dawsonjon/PicoRX/simulations/qsd_animation/fft_animation.gif

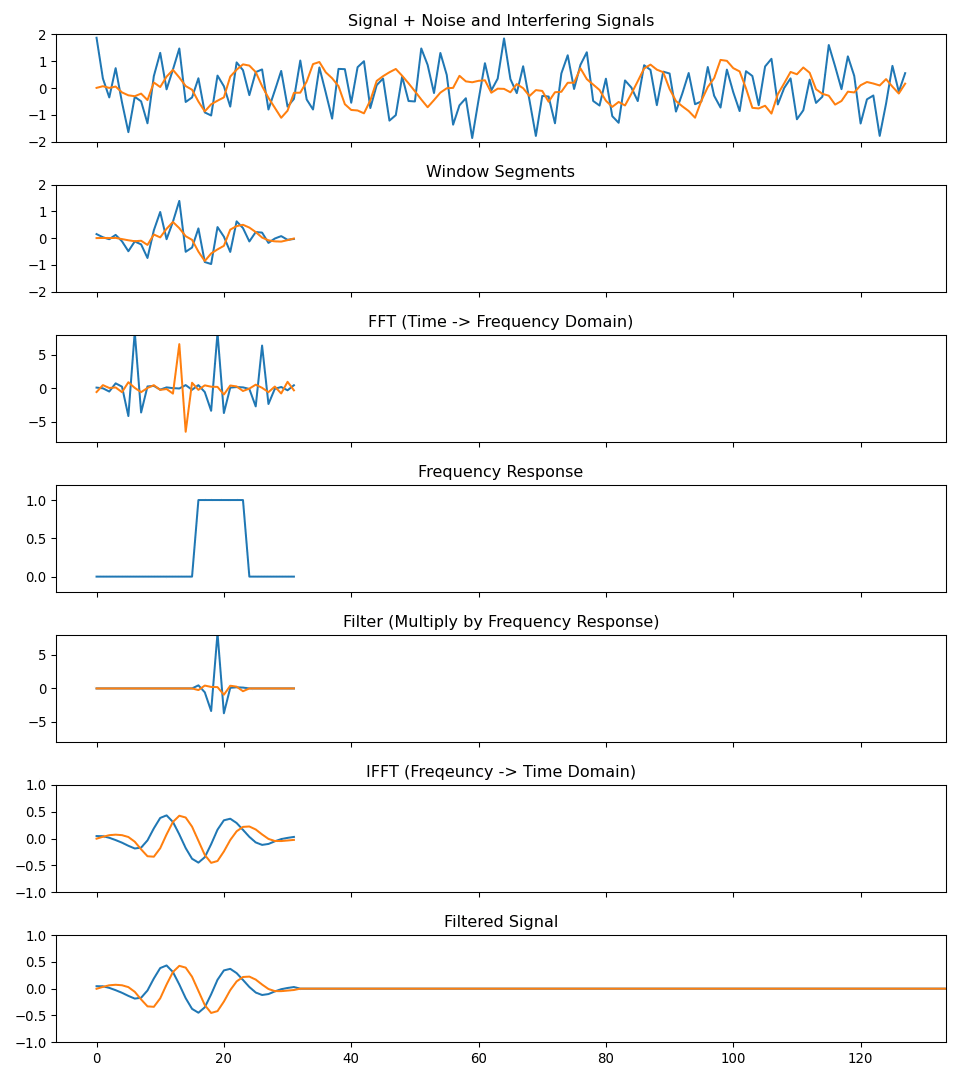
simulations/qsd_animation/fft_animation.gif
