dawsonjon/PicoRX/PCB/concept/concept.kicad_sch

## KiCad design PCB/concept/concept.kicad_sch (2026-02-28)

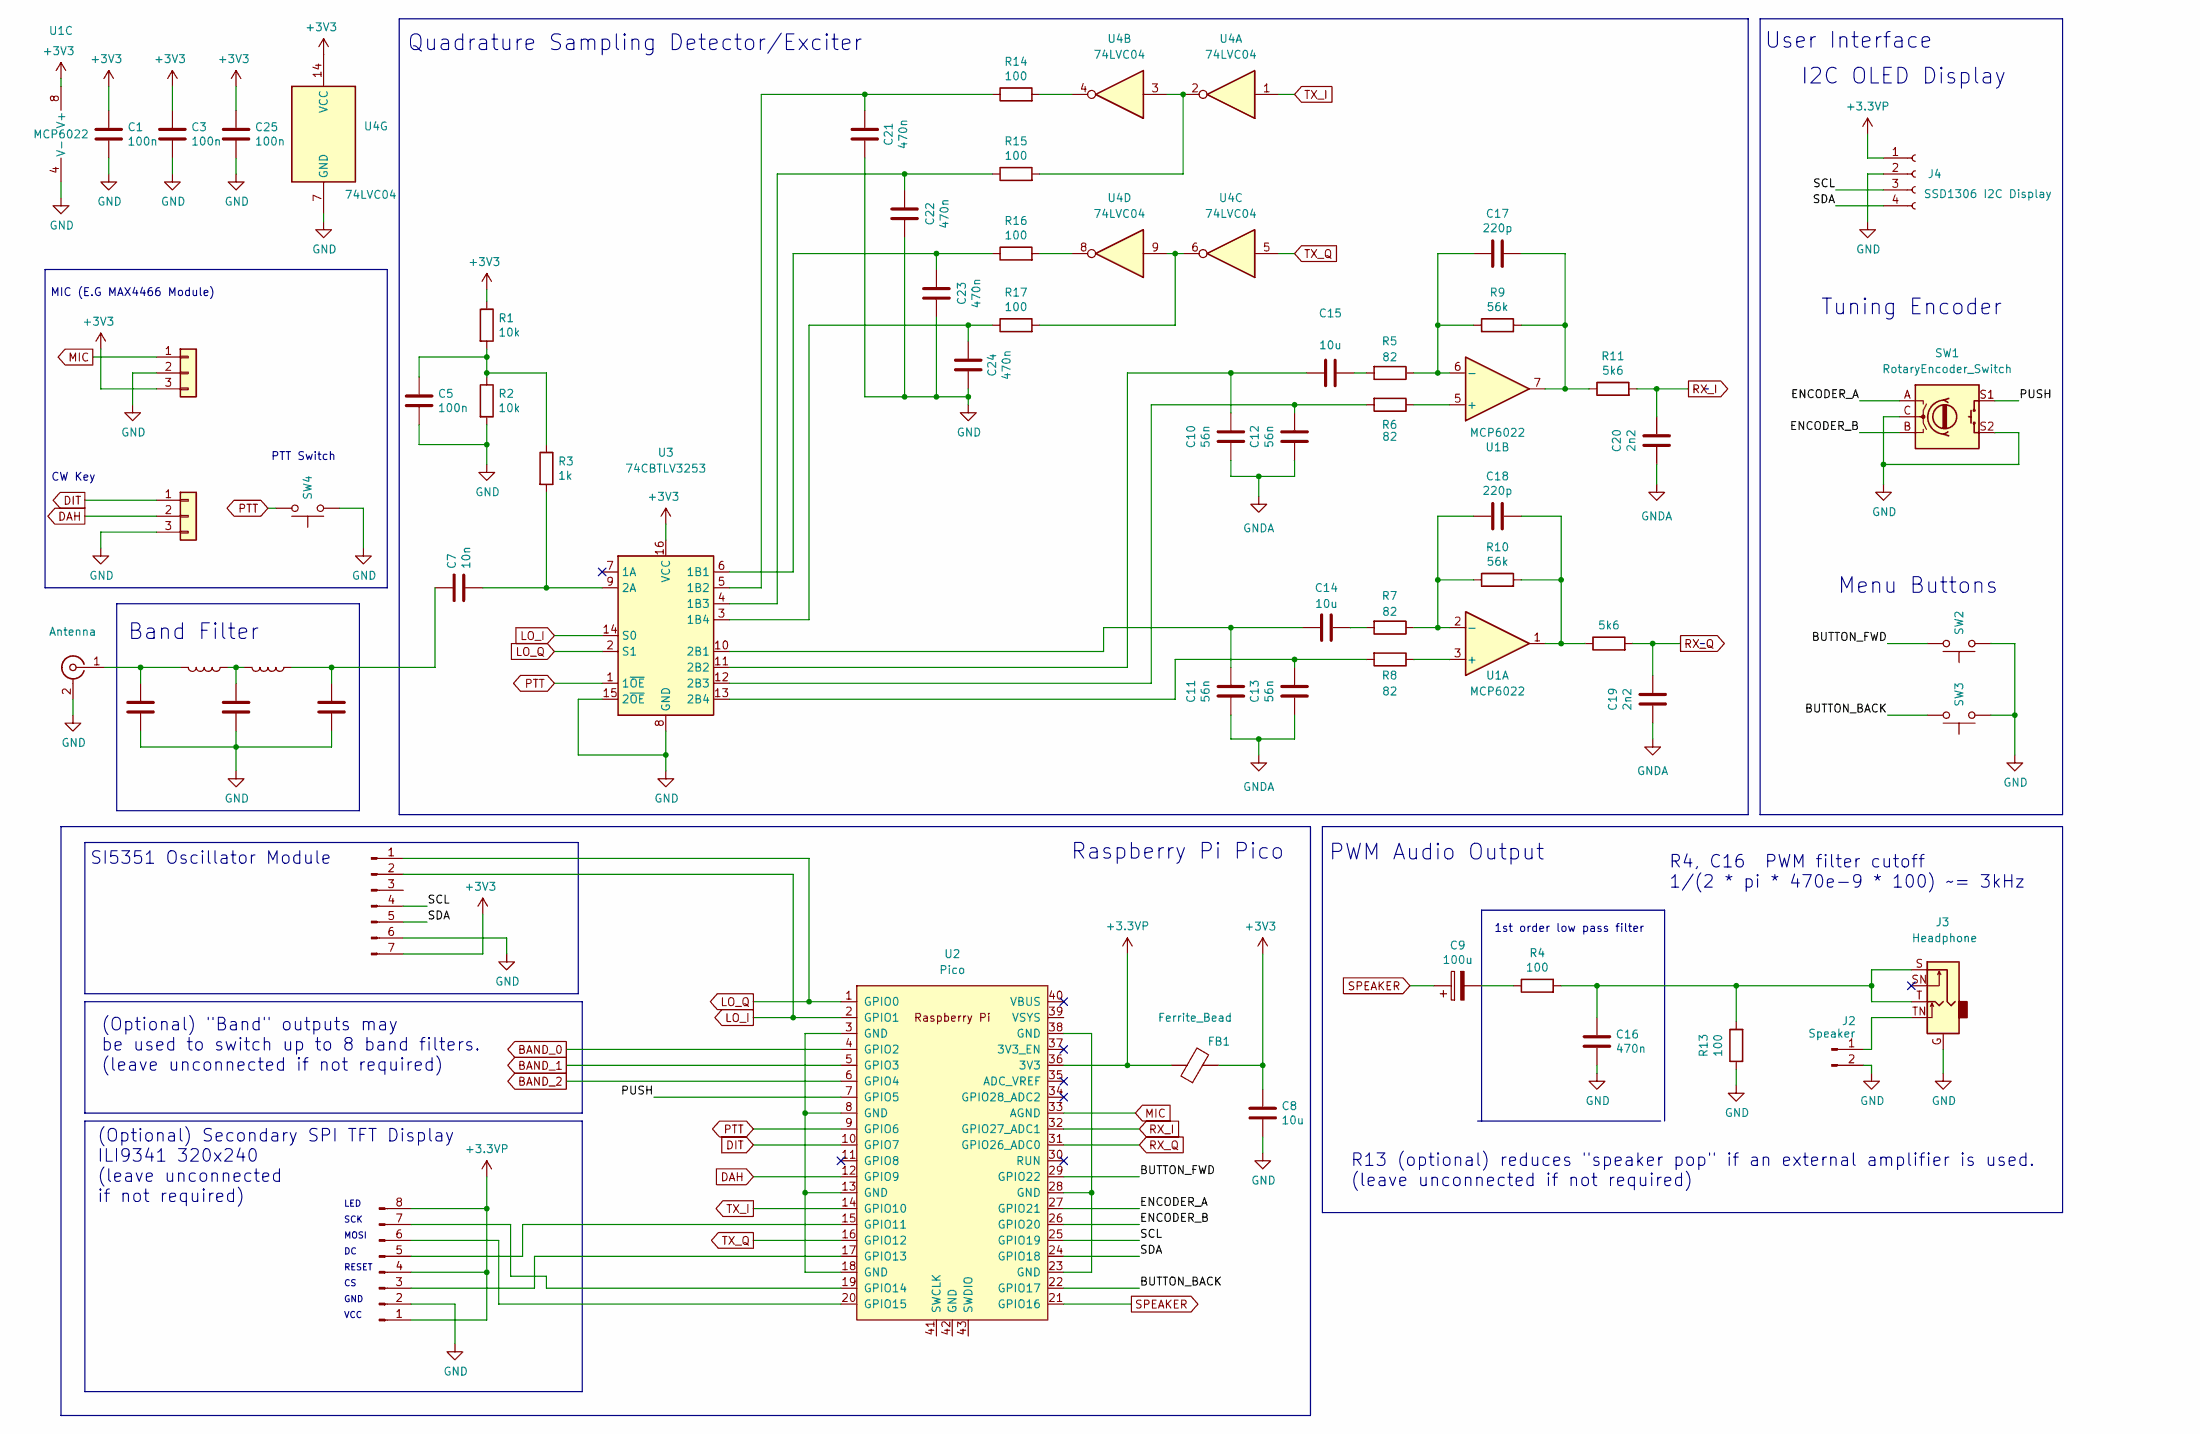
[picture p25: schematic concept.kicad_sch]

Parts:
C1, C3, C5, C25: 100n; C_0805_2012Metric
C2, C6: 680p; C_0805_2012Metric
C4: 1n; C_0805_2012Metric
C7: 10n; C_0805_2012Metric
C8, C14, C15: 10u; C_0805_2012Metric
C9: 100u; CP_EIA-3528-21_Kemet-B
C10, C11, C12, C13: 56n; C_0805_2012Metric
C16, C21, C22, C23, C24: 470n; C_0805_2012Metric
C17, C18: 220p; C_0805_2012Metric
C19, C20: 2n2; C_0805_2012Metric
FB1: Ferrite_Bead; L_0805_2012Metric
J1: Antenna; SMA_Samtec_SMA-J-P-X-ST-EM1_EdgeMount
J2: Speaker; PinHeader_1x02_P2.54mm_Vertical
J3: Headphone; jack3.5mm switched
J4: SSD1306 I2C Display; SDD1306
J5: Conn_01x08_Pin
J6: Conn_01x07_Pin
J7, J8: Conn_01x03
L1, L2: 330n; L_0805_2012Metric_Pad1.05x1.20mm_HandSolder
R1, R2: 10k; R_0805_2012Metric
R3: 1k; R_0805_2012Metric
R4, R13, R14, R15, R16, R17: 100; R_0805_2012Metric
R5, R6, R7, R8: 82; R_0805_2012Metric
R9, R10: 56k; R_0805_2012Metric
R11, R12: 5k6; R_0805_2012Metric
SW1: RotaryEncoder_Switch; RotaryEncoder_Alps_EC11E-Switch_Vertical_H20mm
SW2, SW3, SW4: SW_Push; SW_Tactile_SPST_Angled_PTS645Vx31-2LFS
U1: MCP6022; MSOP-8-1EP_3x3mm_P0.65mm_EP1.68x1.88mm
U2: Pico; RPi_Pico_SMD_TH
U3: 74CBTLV3253; SOIC-16_3.9x9.9mm_P1.27mm
U4: 74LVC04

Connections:
+3.3VP: FB1.1, J4.1, J5.1, J5.4, J5.8, U2.36 (3V3)
+3V3: C1.1, C3.1, C8.1, C25.1, FB1.2, J6.7, J7.3, R1.1, U1.8 (V+), U3.16 (VCC), U4.14 (VCC)
BAND_0: U2.4 (GPIO2)
BAND_1: U2.5 (GPIO3)
BAND_2: U2.6 (GPIO4)
BUTTON_BACK: SW3.2, U2.22 (GPIO17)
BUTTON_FWD: SW2.2, U2.29 (GPIO22)
DAH: J8.2, U2.12 (GPIO9)
DIT: J8.1, U2.10 (GPIO7)
ENCODER_A: SW1.A, U2.27 (GPIO21)
ENCODER_B: SW1.B, U2.26 (GPIO20)
GND: C1.2, C2.1, C3.2, C4.1, C5.2, C6.1, C8.2, C16.2, C21.1, C22.1, C23.1, C24.1, C25.2, J1.2 (Ext), J2.2, J3.G, J4.2, J5.2, J6.6, J7.2, J8.3, R2.2, R13.1, SW1.C, SW1.S2, SW2.1, SW3.1, SW4.1, U1.4 (V-), U3.8 (GND), U3.15 (2~OE), U4.7 (GND)
GNDA: C10.1, C11.1, C12.1, C13.1, C19.1, C20.1
LO_I: J6.2, U2.2 (GPIO1), U3.14 (S0)
LO_Q: J6.1, U2.1 (GPIO0), U3.2 (S1)
MIC: J7.1, U2.33 (AGND)
unnamed: C2.2, J1.1 (In), L1.2
unnamed: C4.2, L1.1, L2.2
unnamed: C5.1, R1.2, R2.1, R3.1
unnamed: C6.2, C7.1, L2.1
unnamed: C7.2, R3.2, U3.9 (2A)
unnamed: C9.2, R4.1
unnamed: C10.2, C15.2, U3.11 (2B2)
unnamed: C11.2, C14.2, U3.10 (2B1)
unnamed: C12.2, R6.2, U3.12 (2B3)
unnamed: C13.2, R8.2, U3.13 (2B4)
unnamed: C14.1, R7.2
unnamed: C15.1, R5.2
unnamed: C16.1, J3.S, J3.T, R4.2, R13.2
unnamed: C17.1, R5.1, R9.1, U1.6 (-)
unnamed: C17.2, R9.2, R11.1, U1.7
unnamed: C18.1, R7.1, R10.1, U1.2 (-)
unnamed: C18.2, R10.2, R12.1, U1.1
unnamed: C21.2, R14.1, U3.5 (1B2)
unnamed: C22.2, R15.1, U3.4 (1B3)
unnamed: C23.2, R16.1, U3.6 (1B1)
unnamed: C24.2, R17.1, U3.3 (1B4)
unnamed: J2.1, J3.TN
unnamed: J5.3, U2.17 (GPIO13)
unnamed: J5.5, U2.15 (GPIO11)
unnamed: J5.6, U2.20 (GPIO15)
unnamed: J5.7, U2.19 (GPIO14)
unnamed: R6.1, U1.5 (+)
unnamed: R8.1, U1.3 (+)
unnamed: R14.2, U4.4
unnamed: R15.2, U4.2, U4.3
unnamed: R16.2, U4.8
unnamed: R17.2, U4.6, U4.9
unnamed: U2.3 (GND), U2.8 (GND), U2.13 (GND), U2.18 (GND)
unnamed: U2.23 (GND), U2.28 (GND), U2.38 (GND)
PTT: SW4.2, U2.9 (GPIO6), U3.1 (1~OE)
PUSH: SW1.S1, U2.7 (GPIO5)
RX_I: C20.2, R11.2, U2.32 (GPIO27_ADC1)
RX_Q: C19.2, R12.2, U2.31 (GPIO26_ADC0)
SCL: J4.3, J6.4, U2.25 (GPIO19)
SDA: J4.4, J6.5, U2.24 (GPIO18)
SPEAKER: C9.1, U2.21 (GPIO16)
TX_I: U2.14 (GPIO10), U4.1
TX_Q: U2.16 (GPIO12), U4.5

Notes on the sheet:
Band Filter
LED
Raspberry Pi Pico
PWM Audio Output
CW Key
SI5351 Oscillator Module
Menu Buttons
I2C OLED Display
R13 (optional) reduces "speaker pop" if an external amplifier is used. (leave unconnected if not required)
PTT Switch
RESET
Quadrature Sampling Detector/Exciter
GND
MIC (E.G MAX4466 Module)
(Optional) "Band" outputs may be used to switch up to 8 band filters. (leave unconnected if not required)
R4, C16 PWM filter cutoff 1/(2 * pi * 470e-9 * 100) ~= 3kHz
1st order low pass filter
Tuning Encoder
VCC
MOSI
SCK
(Optional) Secondary SPI TFT Display ILI9341 320x240 (leave unconnected if not required)
User Interface
