dawsonjon/PicoRX/PCB/pico_rx/Bandpass.kicad_sch

## KiCad design PCB/pico_rx/Bandpass.kicad_sch (2023-07-05)

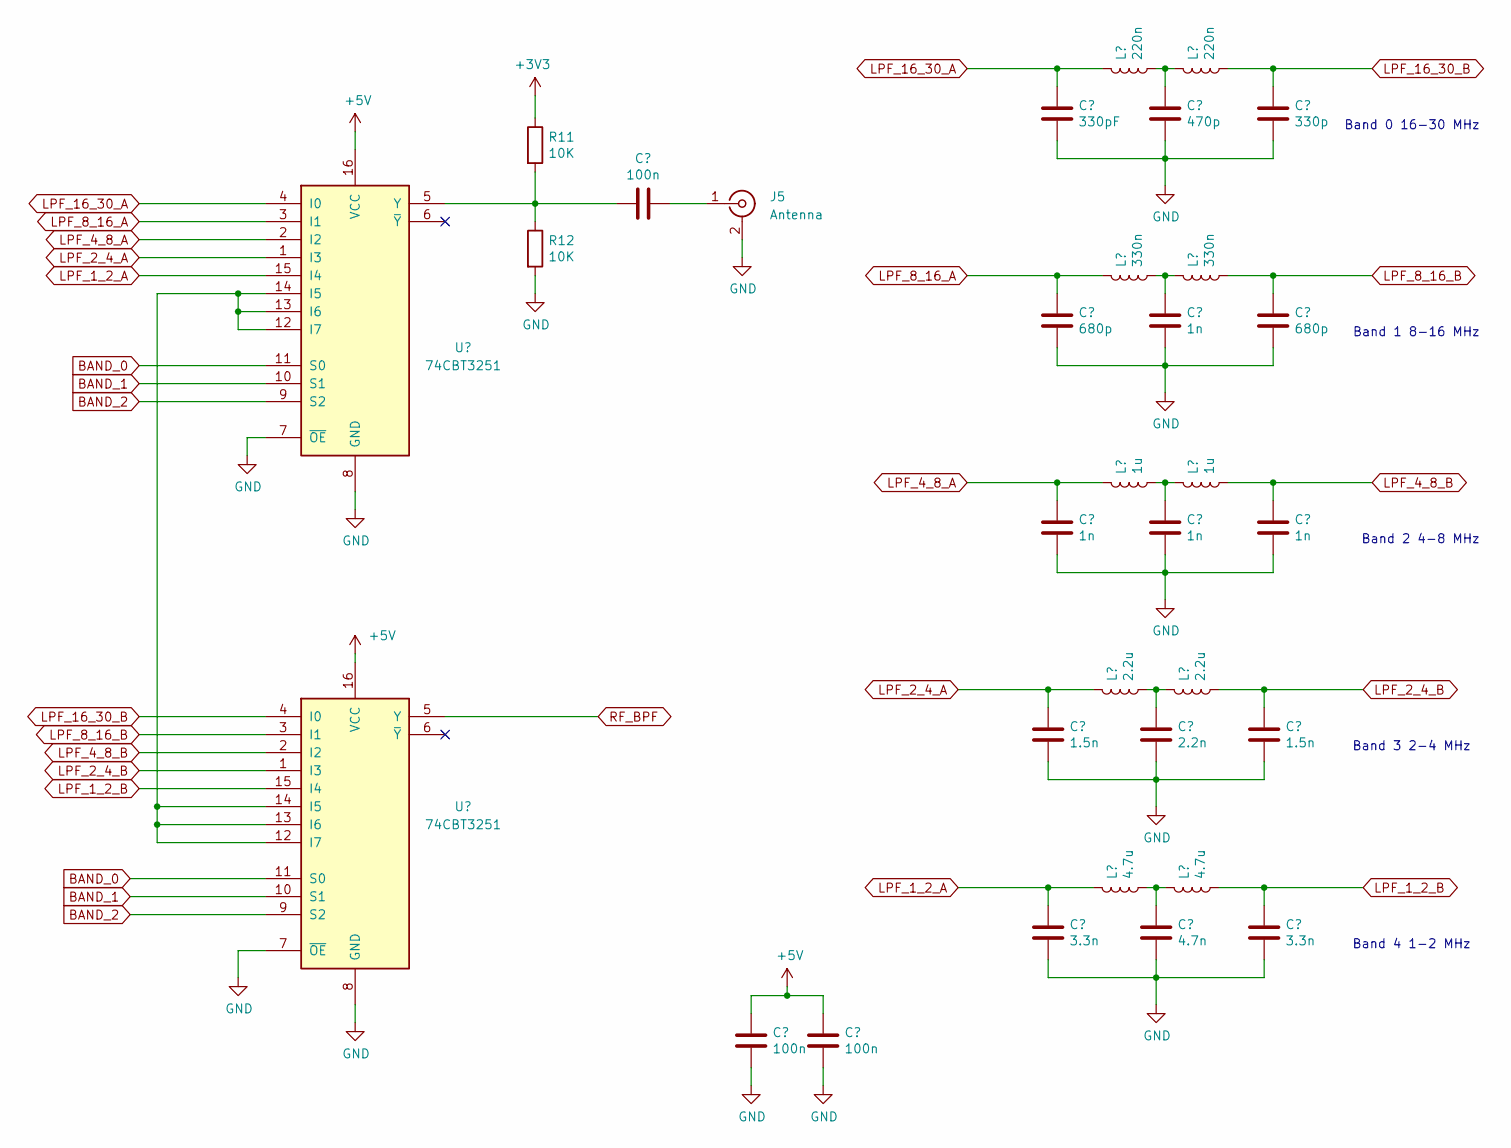
[picture p26: schematic Bandpass.kicad_sch]

Parts:
C1, C2, C3: 100n; C_0805_2012Metric
C6, C9: 680p; C_0805_2012Metric
C7, C13, C14, C15: 1n; C_0805_2012Metric
C8: 330pF; C_0805_2012Metric
C12: 470p; C_0805_2012Metric
C16: 330p; C_0805_2012Metric
C19, C22: 1.5n; C_0805_2012Metric
C21: 2.2n; C_0805_2012Metric
C36, C38: 3.3n; C_0805_2012Metric
C37: 4.7n; C_0805_2012Metric
J5: Antenna; SMA_Amphenol_132289_EdgeMount
L1, L2: 330n; L_0805_2012Metric_Pad1.05x1.20mm_HandSolder
L3, L4: 1u; L_0805_2012Metric_Pad1.05x1.20mm_HandSolder
L5, L13: 220n; L_0805_2012Metric_Pad1.05x1.20mm_HandSolder
L6, L7: 2.2u; L_0805_2012Metric_Pad1.05x1.20mm_HandSolder
L8, L9: 4.7u; L_0805_2012Metric_Pad1.05x1.20mm_HandSolder
R11, R12: 10K; R_0805_2012Metric
U1, U2: 74CBT3251; SOIC-16_3.9x9.9mm_P1.27mm

Connections:
+3V3: R11.1
+5V: C2.1, C3.1, U1.16 (VCC), U2.16 (VCC)
BAND_0: U1.11 (S0), U2.11 (S0)
BAND_1: U1.10 (S1), U2.10 (S1)
BAND_2: U1.9 (S2), U2.9 (S2)
GND: C2.2, C3.2, C6.1, C7.1, C8.1, C9.1, C12.1, C13.1, C14.1, C15.1, C16.1, C19.1, C21.1, C22.1, C36.1, C37.1, C38.1, J5.2 (Ext), R12.2, U1.7 (~OE), U1.8 (GND), U2.7 (~OE), U2.8 (GND)
LPF_1_2_A: C36.2, L8.2, U1.15 (I4)
LPF_1_2_B: C38.2, L9.1, U2.15 (I4)
LPF_2_4_A: C19.2, L6.2, U1.1 (I3)
LPF_2_4_B: C22.2, L7.1, U2.1 (I3)
LPF_4_8_A: C13.2, L3.2, U1.2 (I2)
LPF_4_8_B: C15.2, L4.1, U2.2 (I2)
LPF_8_16_A: C6.2, L1.2, U1.3 (I1)
LPF_8_16_B: C9.2, L2.1, U2.3 (I1)
LPF_16_30_A: C8.2, L13.2, U1.4 (I0)
LPF_16_30_B: C16.2, L5.1, U2.4 (I0)
unnamed: C1.1, J5.1 (In)
unnamed: C1.2, R11.2, R12.1, U1.5 (Y)
unnamed: C7.2, L1.1, L2.2
unnamed: C12.2, L5.2, L13.1
unnamed: C14.2, L3.1, L4.2
unnamed: C21.2, L6.1, L7.2
unnamed: C37.2, L8.1, L9.2
unnamed: U1.12 (I7), U1.13 (I6), U1.14 (I5), U2.12 (I7), U2.13 (I6), U2.14 (I5)
RF_BPF: U2.5 (Y)

Notes on the sheet:
Band 2 4-8 MHz
Band 4 1-2 MHz
Band 1 8-16 MHz
Band 3 2-4 MHz
Band 0 16-30 MHz
