dawsonjon/PicoRX/tusb_config.h

/*
 * The MIT License (MIT)
 *
 * Copyright (c) 2019 Ha Thach (tinyusb.org)
 *
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
 */

#ifndef _TUSB_CONFIG_H_
#define _TUSB_CONFIG_H_

#include "usb_descriptors.h"

#ifdef __cplusplus
extern "C" {
#endif

//--------------------------------------------------------------------
// COMMON CONFIGURATION
//--------------------------------------------------------------------

// defined by compiler flags for flexibility
#ifndef CFG_TUSB_MCU
#error CFG_TUSB_MCU must be defined
#endif

#if CFG_TUSB_MCU == OPT_MCU_LPC43XX || CFG_TUSB_MCU == OPT_MCU_LPC18XX || CFG_TUSB_MCU == OPT_MCU_MIMXRT10XX
#define CFG_TUSB_RHPORT0_MODE       (OPT_MODE_DEVICE | OPT_MODE_HIGH_SPEED)
#else
#define CFG_TUSB_RHPORT0_MODE       OPT_MODE_DEVICE
#endif

#ifndef CFG_TUSB_OS
#define CFG_TUSB_OS                 OPT_OS_NONE
#endif

#ifndef CFG_TUSB_DEBUG
#define CFG_TUSB_DEBUG              0
#endif

// CFG_TUSB_DEBUG is defined by compiler in DEBUG build
// #define CFG_TUSB_DEBUG           0

/* USB DMA on some MCUs can only access a specific SRAM region with restriction on alignment.
 * Tinyusb use follows macros to declare transferring memory so that they can be put
 * into those specific section.
 * e.g
 * - CFG_TUSB_MEM SECTION : __attribute__ (( section(".usb_ram") ))
 * - CFG_TUSB_MEM_ALIGN   : __attribute__ ((aligned(4)))
 */
#ifndef CFG_TUSB_MEM_SECTION
#define CFG_TUSB_MEM_SECTION
#endif

#ifndef CFG_TUSB_MEM_ALIGN
#define CFG_TUSB_MEM_ALIGN          __attribute__ ((aligned(4)))
#endif

//--------------------------------------------------------------------
// DEVICE CONFIGURATION
//--------------------------------------------------------------------

#ifndef CFG_TUD_ENDPOINT0_SIZE
#define CFG_TUD_ENDPOINT0_SIZE    (64)
#endif

//------------- CLASS -------------//
#define CFG_TUD_CDC               1
#define CFG_TUD_MSC               0
#define CFG_TUD_HID               0
#define CFG_TUD_MIDI              0
#define CFG_TUD_AUDIO             1
#define CFG_TUD_VENDOR            0

//--------------------------------------------------------------------
// AUDIO CLASS DRIVER CONFIGURATION
//--------------------------------------------------------------------

// Have a look into audio_device.h for all configurations

#define CFG_TUD_AUDIO_FUNC_1_SAMPLE_RATE                              (15000) // make sure this matches rx_definitions.h:audio_sample_rate
#define CFG_TUD_AUDIO_FUNC_1_DESC_LEN                                 TUD_AUDIO_PICORX_DESC_LEN
#define CFG_TUD_AUDIO_FUNC_1_N_AS_INT                                 1                                       // Number of Standard AS Interface Descriptors (4.9.1) defined per audio function - this is required to be able to remember the current alternate settings of these interfaces - We restrict us here to have a constant number for all audio functions (which means this has to be the maximum number of AS interfaces an audio function has and a second audio function with less AS interfaces just wastes a few bytes)
#define CFG_TUD_AUDIO_FUNC_1_CTRL_BUF_SZ                              64                                      // Size of control request buffer

#define CFG_TUD_AUDIO_ENABLE_EP_IN                                    1
#define CFG_TUD_AUDIO_FUNC_1_N_BYTES_PER_SAMPLE_TX                    2                                       // Driver gets this info from the descriptors - we define it here to use it to setup the descriptors and to do calculations with it below
#define CFG_TUD_AUDIO_FUNC_1_N_CHANNELS_TX                            2                                       // Driver gets this info from the descriptors - we define it here to use it to setup the descriptors and to do calculations with it below - be aware: for different number of channels you need another descriptor!
#define CFG_TUD_AUDIO_EP_SZ_IN                                        TUD_AUDIO_EP_SIZE(CFG_TUD_AUDIO_FUNC_1_SAMPLE_RATE, CFG_TUD_AUDIO_FUNC_1_N_BYTES_PER_SAMPLE_TX, CFG_TUD_AUDIO_FUNC_1_N_CHANNELS_TX)
#define CFG_TUD_AUDIO_FUNC_1_EP_IN_SZ_MAX                             CFG_TUD_AUDIO_EP_SZ_IN                  // Maximum EP IN size for all AS alternate settings used
#define CFG_TUD_AUDIO_FUNC_1_EP_IN_SW_BUF_SZ                          (TUD_OPT_HIGH_SPEED ? 16 : 2) * CFG_TUD_AUDIO_EP_SZ_IN

// CDC FIFO size of TX and RX
#define CFG_TUD_CDC_RX_BUFSIZE                    64
#define CFG_TUD_CDC_TX_BUFSIZE                    64

#ifdef __cplusplus
}
#endif

#endif /* _TUSB_CONFIG_H_ */
