dawsonjon/PicoRX/src/rx_dsp.cpp

#include "rx_dsp.h"
#include "rx_definitions.h"
#include "fft_filter.h"
#include "utils.h"
#include "pico/stdlib.h"
#include "cic_corrections.h"

#include <math.h>
#include <cstdio>
#include <algorithm>

static const int16_t deemph_taps[2][3] = {{14430, 14430, -3909}, {10571, 10571, -11626}};
int16_t __not_in_flash_func(rx_dsp :: apply_deemphasis)(int16_t x)
{
if (deemphasis == 0) return x;

  static int16_t x1 = 0;
  static int16_t y1 = 0;
  static int16_t err = 0;

  const size_t i = deemphasis - 1;

  int32_t y = ((int32_t)x * deemph_taps[i][0]) +
              ((int32_t)x1 * deemph_taps[i][1]) -
              ((int32_t)y1 * deemph_taps[0][2]) + err;

  if (y > 0x1FFFFFFFL) {
    y = 0x1FFFFFFFL;
  }
  if (y < -0x20000000L) {
    y = -0x20000000L;
  }

  err = y & ((1 << 15) - 1);
  y >>= 15;
  x1 = x;
  y1 = y;
  return y;
}

int16_t __not_in_flash_func(rx_dsp ::apply_treble)(int16_t x) {
  static const int32_t treble_taps[4][2][3] = {
      {{26363, -36747, 14207}, {16383, -19828, 7267}},
      {{42359, -62303, 24741}, {16383, -18062, 6476}},
      {{67860, -104422, 42534}, {16383, -16114, 5703}},
      {{108241, -173031, 72157}, {16383, -13987, 4972}}};

  static int16_t x1 = 0;
  static int16_t y1 = 0;
  static int16_t x2 = 0;
  static int16_t y2 = 0;
  static int16_t err = 0;

  if (treble == 0) return x;

  const uint8_t i = treble - 1;

  x >>= 1;
  int32_t y = ((int32_t)x * treble_taps[i][0][0]) +
              ((int32_t)x1 * treble_taps[i][0][1]) +
              ((int32_t)x2 * treble_taps[i][0][2]) + err;
  y -= ((int32_t)y1 * treble_taps[i][1][1]) +
       ((int32_t)y2 * treble_taps[i][1][2]);

  if (y > 0xFFFFFFFL) {
    y = 0xFFFFFFFL;
  }
  if (y < -0x10000000L) {
    y = -0x10000000L;
  }

  err = y & ((1 << 14) - 1);
  y >>= 14;

  x2 = x1;
  x1 = x;
  y2 = y1;
  y1 = y;
  return y << 1;
}

int16_t __not_in_flash_func(rx_dsp ::apply_bass)(int16_t x) {
  static const int32_t bass_taps[4][2][3] = {
      {{16808, -30178, 13691}, {16383, -30248, 14045}},
      {{17253, -30437, 13616}, {16383, -30584, 14338}},
      {{17728, -30637, 13490}, {16383, -30876, 14596}},
      {{18245, -30777, 13313}, {16383, -31129, 14824}}};

  static int16_t x1 = 0;
  static int16_t y1 = 0;
  static int16_t x2 = 0;
  static int16_t y2 = 0;
  static int16_t err = 0;

  if (bass == 0) return x;

  const uint8_t i = bass - 1;

  x >>= 1;
  int32_t y = ((int32_t)x * bass_taps[i][0][0]) +
              ((int32_t)x1 * bass_taps[i][0][1]) +
              ((int32_t)x2 * bass_taps[i][0][2]) + err;
  y -= ((int32_t)y1 * bass_taps[i][1][1]) + ((int32_t)y2 * bass_taps[i][1][2]);

  if (y > 0xFFFFFFFL) {
    y = 0xFFFFFFFL;
  }
  if (y < -0x10000000L) {
    y = -0x10000000L;
  }

  err = y & ((1 << 14) - 1);
  y >>= 14;

  x2 = x1;
  x1 = x;
  y2 = y1;
  y1 = y;
  return y << 1;
}

void __not_in_flash_func(rx_dsp ::apply_impulse_blanker)(int16_t &i, int16_t &q,
                                                         uint16_t mag) {
  static uint32_t avg_g = 32767;
  static uint32_t avg_mag;
  const uint32_t thres_lut[6] = {98301, 91748, 85194, 78641,
                                 72087, 65534};  // 3.0 to 2.0 in 0.2 steps

  if(impulse_threshold == 0)
  {
    return;
  }

  avg_mag += mag - (avg_mag / 4096);
  const uint32_t a_mag = avg_mag / 4096;

  const uint32_t thr = thres_lut[impulse_threshold - 1];

  uint32_t g = 32767;
  if (mag > ((a_mag * thr) >> 15)) {
    g = (a_mag << 15) / mag;
  }
  avg_g += g - avg_g / 8;
  g = avg_g / 8;

  if (g < 32767) {
    i = (g * i) >> 15;
    q = (g * q) >> 15;
  }
}

static uint32_t __not_in_flash_func(intsqrt)(const uint32_t n) {
    uint8_t shift = 32u;
    shift += shift & 1; // round up to next multiple of 2

    uint32_t result = 0;

    do {
        shift -= 2;
        result <<= 1; // leftshift the result to make the next guess
        result |= 1;  // guess that the next bit is 1
        result ^= result * result > (n >> shift); // revert if guess too high
    } while (shift != 0);

    return result;
}

void inline rx_dsp :: iq_imbalance_correction(int16_t &i, int16_t &q)
{
    if (iq_correction)
    {
      static uint16_t index = 0;
      static int32_t theta1 = 0;
      static int32_t theta2 = 0;
      static int32_t theta3 = 0;

      theta1 += ((i < 0) ? -q : q);
      theta2 += ((i < 0) ? -i : i);
      theta3 += ((q < 0) ? -q : q);

      static int32_t c1 = 0;
      static int32_t c2 = 0;
      if (++index == 512)
      {
        static int64_t theta1_filtered = 0;
        static int64_t theta2_filtered = 0;
        static int64_t theta3_filtered = 0;
        theta1_filtered = theta1_filtered - (theta1_filtered >> 5) + (-theta1 >> 5);
        theta2_filtered = theta2_filtered - (theta2_filtered >> 5) + (theta2 >> 5);
        theta3_filtered = theta3_filtered - (theta3_filtered >> 5) + (theta3 >> 5);

        //try to constrain square to less than 32 bits.
        //Assue that i/q used full int16_t range.
        //Accumulating 512 samples adds 9 bits of growth, so remove 18 after square.
        const int64_t theta1_squared = (theta1_filtered * theta1_filtered) >> 18;
        const int64_t theta2_squared = (theta2_filtered * theta2_filtered) >> 18;
        const int64_t theta3_squared = (theta3_filtered * theta3_filtered) >> 18;

        c1 = (theta1_filtered << 15)/theta2_filtered;
        c2 = intsqrt(((theta3_squared - theta1_squared) << 30)/theta2_squared);

        theta1 = 0;
        theta2 = 0;
        theta3 = 0;
        index = 0;
      }

      q += ((int32_t)i * c1) >> 15;
      i = ((int32_t)i * c2) >> 15;
    }
}

uint16_t __not_in_flash_func(rx_dsp :: process_block)(uint16_t samples[], int16_t audio_samples[], ring_buffer_t *iq_samples)
{

  uint16_t decimated_index = 0;
  int16_t iq[2 * adc_block_size / cic_decimation_rate];

  for(uint16_t idx=0; idx<adc_block_size; idx++)
  {
      //convert to signed representation
      const int16_t raw_sample = samples[idx];

      //work out which samples are i and q
      int16_t i = ((idx&1)^1^swap_iq)*raw_sample;//even samples contain i data
      int16_t q = ((idx&1)^swap_iq)*raw_sample;//odd samples contain q data

      //reduce sample rate by a factor of 16
      if(decimate(i, q))
      {

        static uint32_t iq_count = 0;
        static int32_t i_accumulator = 0;
        static int32_t q_accumulator = 0;
        static int16_t i_avg = 0;
        static int16_t q_avg = 0;
        i_accumulator += i;
        q_accumulator += q;
        if (++iq_count == 2048) //power of 2 avoids division
        {
          i_avg = i_accumulator / 2048;
          q_avg = q_accumulator / 2048;
          i_accumulator = 0;
          q_accumulator = 0;
          iq_count = 0;
        }
        i -= i_avg;
        q -= q_avg;

        iq_imbalance_correction(i, q);

        //Apply frequency shift (move tuned frequency to DC)
        frequency_shift(i, q);

        #ifdef MEASURE_DC_BIAS
        static int64_t bias_measurement = 0;
        static int32_t num_bias_measurements = 0;
        if(num_bias_measurements == 100000) {
          printf("DC BIAS x 100 %lli\n", bias_measurement/1000);
          num_bias_measurements = 0;
          bias_measurement = 0;
        }
        else {
          num_bias_measurements++;
          bias_measurement += i;
        }
        #endif

        iq[decimated_index] = i;
        iq[decimated_index + 1] = q;
        decimated_index+=2;
      }
  }

  //fft filter decimates a further 2x
  //if the capture buffer isn't in use, fill it
  filter_control.capture = sem_try_acquire(&spectrum_semaphore);
  capture_filter_control = filter_control;
  fft_filter_inst.process_sample(iq, filter_control, capture);
  if(filter_control.capture) sem_release(&spectrum_semaphore);

  for(uint16_t idx=0; idx<adc_block_size/decimation_rate; idx++)
  {
    int16_t i = iq[2 * idx];
    int16_t q = iq[2 * idx + 1];

    uint32_t complex_sample = (uint32_t)i << 16 | ((uint32_t)q & 0xffff);
    queue_try_add(&data_queue, (void*)&complex_sample);

    //Measure amplitude (for signal strength indicator)
    uint16_t magnitude;
    int16_t _phase;
    rectangular_2_polar(i, q, &magnitude, &_phase);

    // Impulse noise blanker
    apply_impulse_blanker(i, q, magnitude);

    //Demodulate to give audio sample
    int32_t audio = demodulate(i, q, magnitude, _phase);

    //De-emphasis
    audio = apply_deemphasis(audio);

    // Bass
    audio = apply_bass(audio);

    // Treble
    audio = apply_treble(audio);

    //Automatic gain control scales signal to use full 16 bit range
    //e.g. -32767 to 32767
    audio = automatic_gain_control(audio);

    //squelch
    audio = squelch(audio);

    //output raw audio
    audio_samples[idx] = audio;
  }

  if (sem_try_acquire(&audio_semaphore)) {
    for (uint16_t idx = 0; idx < adc_block_size / decimation_rate; idx+=4) {
      audio_capture[audio_capture_idx * 16 + (idx / 4)] = audio_samples[idx];
    }
    audio_capture_idx++;
    if (audio_capture_idx == 8) {
      audio_capture_idx = 0;
    }
    sem_release(&audio_semaphore);
  }

  if (iq_samples) {
    ring_buffer_push_ovr(
        iq_samples, (uint8_t *)iq,
        2 * sizeof(int16_t) * adc_block_size / decimation_rate);
  }

  //average over the number of samples
  signal_amplitude = (filter_control.magnitude_sum * decimation_rate)/adc_block_size;

  return adc_block_size/decimation_rate;
}

void __not_in_flash_func(rx_dsp :: frequency_shift)(int16_t &i, int16_t &q)
{
    //Apply frequency shift (move tuned frequency to DC)
    const uint16_t scaled_phase = (phase >> 21);
    const int16_t rotation_i =  sin_table[(scaled_phase+512u) & 0x7ff]; //32 - 21 = 11MSBs
    const int16_t rotation_q = -sin_table[scaled_phase];

    phase += frequency;
    //truncating fractional bits introduces bias, but it is more efficient to remove it after decimation
    int32_t bias = (1<<14);
    const int16_t i_shifted = (((int32_t)i * rotation_i) - ((int32_t)q * rotation_q) + bias) >> 15;
    const int16_t q_shifted = (((int32_t)q * rotation_i) + ((int32_t)i * rotation_q) + bias) >> 15;

    i = i_shifted;
    q = q_shifted;
}

bool __not_in_flash_func(rx_dsp :: decimate)(int16_t &i, int16_t &q)
{
      static int32_t integratori4d5 = 0;
      static int32_t integratorq4d5 = 0;

      //CIC decimation filter
      //implement integrator stages
      integratori1 += i;
      integratorq1 += q;
      integratori2 += integratori1;
      integratorq2 += integratorq1;
      integratori3 += integratori2;
      integratorq3 += integratorq2;
      integratori4 += integratori3;
      integratorq4 += integratorq3;

      decimate_count++;
      if(decimate_count == (cic_decimation_rate-5))
      {
        integratori4d5 = integratori4;
        integratorq4d5 = integratorq4;
      }
      else if(decimate_count >= cic_decimation_rate)
      {
        decimate_count = 0;

        //implement comb stages
        const int32_t combi1 = integratori4-delayi0;
        const int32_t combq1 = integratorq4-delayq0;
        const int32_t combi2 = combi1-delayi1;
        const int32_t combq2 = combq1-delayq1;
        const int32_t combi3 = combi2-delayi2;
        const int32_t combq3 = combq2-delayq2;
        const int32_t combi4 = combi3-delayi3;
        const int32_t combq4 = combq3-delayq3;
        delayi0 = integratori4d5;
        delayq0 = integratorq4d5;
        delayi1 = combi1;
        delayq1 = combq1;
        delayi2 = combi2;
        delayq2 = combq2;
        delayi3 = combi3;
        delayq3 = combq3;

        //remove bit growth, but keep some extra bits since noise floor is now lower
        i = combi4>>(cic_bit_growth-extra_bits);
        q = combq4>>(cic_bit_growth-extra_bits);

        return true;
      }

      return false;
}

// For the formulas see 'PicoRX/simulations/am_sync_des.py:pll_3rd_order_des'
// PLL loop bandwidth: 30Hz
#define AMSYNC_NUM_TAPS (3)
#define AMSYNC_B0 (1160)
#define AMSYNC_B1 (-2306)
#define AMSYNC_B2 (1146)
#define AMSYNC_A0 (32767)
#define AMSYNC_A1 (-65534)
#define AMSYNC_A2 (32767)
#define AMSYNC_PI (102941)
#define AMSYNC_ONE (32767)
#define AMSYNC_MAX (262143)
#define AMSYNC_ERR_SCALE (3)
#define AMSYNC_PHI_SCALE (101)
#define AMSYNC_FRACTION_BITS (15)
#define AMSYNC_BASE_FRACTION_BITS (15)
#define AMSYNC_FILT_BITS (15)
#define AMSYNC_FILT_ONE (32767)

inline int32_t wrap(int32_t x) {
  if (x > AMSYNC_PI) {
    x = -AMSYNC_PI + (x % AMSYNC_PI);
  } else if (x < -AMSYNC_PI) {
    x = AMSYNC_PI + (x % AMSYNC_PI);
  }
  return x;
}

void rx_dsp::amsync_reset(void) { amsync = {0, 0, 0, 0, 0, 0}; }

int16_t __not_in_flash_func(rx_dsp :: demodulate)(int16_t i, int16_t q, uint16_t magnitude, int16_t _phase)
{
    const int16_t _frequency = _phase - last_phase;
    last_phase = _phase;

    frequency_accumulator += _frequency;
    frequency_count ++;

    if(mode == AM)
    {
        const int16_t amplitude = magnitude;
        //measure DC using first order IIR low-pass filter
        audio_dc = amplitude+(audio_dc - (audio_dc >> 5));
        //subtract DC component
        return amplitude - (audio_dc >> 5);
    }
    else if(mode == AMSYNC)
    {
      size_t idx = (amsync.phase_locked / AMSYNC_PHI_SCALE);

      if (amsync.phase_locked < 0) {
        idx = 2048 + idx;
      }

      // VCO
      const int32_t vco_i = sin_table[(idx + 512u) & 0x7ffu];
      const int32_t vco_q = sin_table[idx & 0x7ffu];

      // Phase Detector
      const int16_t synced_i = (i * vco_i + q * vco_q) >> AMSYNC_BASE_FRACTION_BITS;
      const int16_t synced_q = (-i * vco_q + q * vco_i) >> AMSYNC_BASE_FRACTION_BITS;

      int16_t phi;
      uint16_t mag;

      rectangular_2_polar(synced_i, synced_q, &mag, &phi);

      const int32_t phi_err = ((int32_t)phi * AMSYNC_ERR_SCALE);

      int32_t y0 = phi_err * AMSYNC_B0 + amsync.x1 * AMSYNC_B1 + amsync.x2 * AMSYNC_B2;
      y0 += amsync.y0_err;
      amsync.y0_err = y0 & AMSYNC_FILT_ONE;
      y0 >>= AMSYNC_FILT_BITS;
      y0 += 2 * amsync.y1 - amsync.y2;
      amsync.y2 = amsync.y1;
      amsync.y1 = y0;
      amsync.x2 = amsync.x1;
      amsync.x1 = phi_err;
      amsync.phase_locked += y0;

      amsync.phase_locked = wrap(amsync.phase_locked);

      // measure DC using first order IIR low-pass filter
      audio_dc = synced_i + (audio_dc - (audio_dc >> 5));
      // subtract DC component
      return synced_i - (audio_dc >> 5);
    }
    else if(mode == FM)
    {
        return _frequency;
    }
    else if(mode == LSB || mode == USB)
    {
        return i;
    }
    else //if(mode==cw)
    {
      cw_sidetone_phase += cw_sidetone_frequency_Hz * 2048 * decimation_rate / adc_sample_rate;
      const int16_t rotation_i =  sin_table[(cw_sidetone_phase + 512u) & 0x7ffu];
      const int16_t rotation_q = -sin_table[cw_sidetone_phase & 0x7ffu];
      return ((i * rotation_i) - (q * rotation_q)) >> 15;
    }
}

int16_t __not_in_flash_func(rx_dsp::squelch)(int16_t audio)
{
    if(signal_amplitude > squelch_threshold)
      squelch_time_ms = to_ms_since_boot(get_absolute_time());
    const uint32_t time_since_active = to_ms_since_boot(get_absolute_time())-squelch_time_ms;

    if(time_since_active < squelch_timeout_ms)
    {
      return audio;
    } else {
      return 0;
    }
}

int16_t __not_in_flash_func(rx_dsp::automatic_gain_control)(int16_t audio_in)
{
    //Use a leaky max hold to estimate audio power
    //             _
    //            | |
    //            | |
    //    audio __| |_____________________
    //            | |
    //            |_|
    //
    //                _____________
    //               /             \_
    //    max_hold  /                \_
    //           _ /                   \_
    //              ^                ^
    //            attack             |
    //                <---hang--->   |
    //                             decay

    // Attack is fast so that AGC reacts fast to increases in power
    // Hang time and decay are relatively slow to prevent rapid gain changes

    static const uint8_t _extra_bits = 16;
    int32_t audio = audio_in;
    const int32_t audio_scaled = audio << _extra_bits;
    if(audio_scaled > max_hold)
    {
      //attack
      max_hold += (audio_scaled - max_hold) >> attack_factor;
      hang_timer = hang_time;
    }
    else if(hang_timer)
    {
      //hang
      hang_timer--;
    }
    else if(max_hold > 0)
    {
      //decay
      max_hold -= max_hold>>decay_factor;
    }

    //calculate gain needed to amplify to full scale
    const int16_t magnitude = max_hold >> _extra_bits;
    const int16_t limit = INT16_MAX; //hard limit
    const int16_t setpoint = limit/2; //about half full scale

    //apply gain
    if(magnitude > 0)
    {
      if(manual_gain_control)
      {
        gain = manual_gain;
      }
      else
      {
        const int16_t agc_gain = setpoint/magnitude;
        gain = std::min(agc_gain, manual_gain);
      }
      if(gain < 1) gain = 1;
      audio *= gain;
    }

    //soft clip (compress)
    if (audio > setpoint)  audio =  setpoint + ((audio-setpoint)>>1);
    if (audio < -setpoint) audio = -setpoint - ((audio+setpoint)>>1);

    //hard clamp
    if (audio > limit)  audio = limit;
    if (audio < -limit) audio = -limit;

    return audio;
}

rx_dsp :: rx_dsp()
{
  //initialise state
  phase = 0;
  frequency=0;
  initialise_luts();
  swap_iq = 0;
  iq_correction = 0;

  //initialise semaphore for spectrum
  set_mode(AM, 2);
  sem_init(&spectrum_semaphore, 1, 1);
  queue_init(&data_queue, 4, 2048);
  set_agc_control(3, 0);
  filter_control.enable_auto_notch = false;
  filter_control.enable_noise_reduction = false;
  filter_control.noise_smoothing = 10;
  filter_control.noise_threshold = 1;
  filter_control.spectrum_smoothing = 1;

  sem_init(&audio_semaphore, 1, 1);

  //clear cic filter
  decimate_count=0;
  integratori1=0; integratorq1=0;
  integratori2=0; integratorq2=0;
  integratori3=0; integratorq3=0;
  integratori4=0; integratorq4=0;
  delayi0=0; delayq0=0;
  delayi1=0; delayq1=0;
  delayi2=0; delayq2=0;
  delayi3=0; delayq3=0;

}

void rx_dsp :: set_auto_notch(bool enable_auto_notch)
{
  filter_control.enable_auto_notch = enable_auto_notch;
}

void rx_dsp :: set_spectrum_smoothing(uint8_t spectrum_smoothing)
{
  filter_control.spectrum_smoothing = spectrum_smoothing;
}

void rx_dsp :: set_noise_reduction(bool enable_noise_reduction, int8_t noise_smoothing, int8_t noise_threshold)
{
  filter_control.enable_noise_reduction = enable_noise_reduction;
  filter_control.noise_smoothing = noise_smoothing;
  filter_control.noise_threshold = noise_threshold;
}

void rx_dsp :: set_deemphasis(uint8_t deemph)
{
  deemphasis = deemph;
}

void rx_dsp ::set_treble(uint8_t tr) {
  if (tr > 4) {
    tr = 4;
  }
  treble = tr;
}

void rx_dsp ::set_bass(uint8_t bs) {
  if (bs > 4) {
    bs = 4;
  }
  bass = bs;
}

void rx_dsp ::set_impulse_threshold(uint8_t it) {
  if (it > 6) {
    it = 6;
  }
  impulse_threshold = it;
}

void rx_dsp :: set_agc_control(uint8_t agc_control, uint8_t agc_gain)
{
  //input fs=480000.000000 Hz
  //decimation=32 x 2
  //fs=15625.000000 Hz
  //Setting Decay Time(s) Factor Attack Time(s) Factor  Hang  Timer
  //======= ============= ====== ============== ======  ====  =====
  //fast        0.151          10       0.001      2    0.1s   1500
  //medium      0.302          11       0.001      2    0.25s  3750
  //slow        0.604          12       0.001      2    1s     15000
  //long        2.414          14       0.001      2    2s     30000


  manual_gain_control = false;
  manual_gain = 1 << (agc_gain);

  switch(agc_control)
  {
      case 0: //fast
        attack_factor=2;
        decay_factor=10;
        hang_time=1500;
        break;

      case 1: //medium
        attack_factor=2;
        decay_factor=11;
        hang_time=3750;
        break;

      case 2: //slow
        attack_factor=2;
        decay_factor=12;
        hang_time=15000;
        break;

      case 3: //long
        attack_factor=2;
        decay_factor=14;
        hang_time=30000;
        break;

      default://manual
        manual_gain_control = true;
        break;
  }
}

void rx_dsp :: set_frequency_offset_Hz(double offset_frequency)
{
  offset_frequency_Hz = offset_frequency;
  const float bin_width = adc_sample_rate/(cic_decimation_rate*256);
  filter_control.fft_bin = offset_frequency/bin_width;
  frequency = ((double)(1ull<<32)*offset_frequency)*cic_decimation_rate/(adc_sample_rate);
}


void rx_dsp :: set_mode(uint8_t val, uint8_t bw)
{
  mode = val;
  //                           AM AMS LSB USB NFM CW
  uint8_t start_bins[6]   =  {  0,  0,  3,  3,  0, 0};

  uint8_t stop_bins[5][6] = {{ 19, 19, 16, 16, 31, 0},  //very narrow
                             { 22, 22, 19, 19, 34, 1},  //narrow
                             { 25, 25, 22, 22, 37, 2},  //normal
                             { 31, 31, 25, 25, 40, 3},  //wide
                             { 63, 63, 28, 28, 43, 4}}; //very wide

  filter_control.lower_sideband = (mode != USB);
  filter_control.upper_sideband = (mode != LSB);
  filter_control.start_bin = start_bins[mode];
  filter_control.stop_bin = stop_bins[bw][mode];
}

void rx_dsp :: set_swap_iq(uint8_t val)
{
  swap_iq = val;
}

void rx_dsp :: set_iq_correction(uint8_t val)
{
  iq_correction = val;
}

void rx_dsp :: set_cw_sidetone_Hz(uint16_t val)
{
  cw_sidetone_frequency_Hz = val;
}

void rx_dsp :: set_gain_cal_dB(uint16_t val)
{
  amplifier_gain_dB = val;
  s9_threshold = full_scale_signal_strength*powf(10.0f, (S9 - full_scale_dBm + amplifier_gain_dB)/20.0f);
}

//set_squelch
void rx_dsp :: set_squelch(uint8_t threshold, uint8_t timeout)
{
  //0-9 = s0 to s9, 10 to 12 = S9+10dB to S9+30dB
  const int16_t thresholds[] = {
    (int16_t)(s9_threshold>>9), //s0
    (int16_t)(s9_threshold>>8), //s1
    (int16_t)(s9_threshold>>7), //s2
    (int16_t)(s9_threshold>>6), //s3
    (int16_t)(s9_threshold>>5), //s4
    (int16_t)(s9_threshold>>4), //s5
    (int16_t)(s9_threshold>>3), //s6
    (int16_t)(s9_threshold>>2), //s7
    (int16_t)(s9_threshold>>1), //s8
    (int16_t)(s9_threshold),    //s9
    (int16_t)(s9_threshold*3),  //s9+10dB
    (int16_t)(s9_threshold*10), //s9+20dB
    (int16_t)(s9_threshold*31), //s9+30dB
  };
  const uint16_t timeouts[] = {
    50, 100, 200, 500, 1000, 2000, 3000, 5000
  };
  squelch_threshold = thresholds[threshold];
  squelch_timeout_ms = timeouts[timeout];
}

int16_t rx_dsp :: get_signal_strength_dBm()
{
  if(signal_amplitude == 0)
  {
    return -130;
  }
  const float signal_strength_dBFS = 20.0*log10f((float)signal_amplitude / full_scale_signal_strength);
  return roundf(full_scale_dBm - amplifier_gain_dB + signal_strength_dBFS);
}

s_filter_control rx_dsp :: get_filter_config()
{
  return capture_filter_control;
}

static inline int8_t freq_bin(uint8_t bin)
{
  return bin > 127 ? bin - 256 : bin;
}

static inline uint8_t fft_shift(uint8_t bin)
{
  return bin ^ 0x80;
}

void rx_dsp :: get_spectrum(uint8_t spectrum[], uint8_t &dB10, uint8_t zoom)
{
  //FFT and magnitude
  sem_acquire_blocking(&spectrum_semaphore);

  //find minimum and maximum values
  const uint16_t lowest_max = 2500u;
  static uint16_t max=65523u;//long term maximum
  uint16_t new_max=0u;
  static uint16_t min=1u;//long term maximum
  uint16_t new_min=65535u;
  for(uint16_t i=0; i<256; ++i)
  {
    const uint16_t magnitude = cic_correct(freq_bin(i), capture_filter_control.fft_bin, capture[i]);
    if(magnitude == 0) continue;
    new_max = std::max(magnitude, new_max);
    new_min = std::min(magnitude, new_min);
  }
  max=new_max;
  min=new_min;
  const float logmin = log10f(min);
  const float logmax = log10f(std::max(max, lowest_max));

  //clamp and convert to log scale 0 -> 255
  uint8_t temp_spectrum[256];
  for(uint16_t i=0; i<256; ++i)
  {
    const uint16_t magnitude = cic_correct(freq_bin(i), capture_filter_control.fft_bin, capture[i]);
    if(magnitude == 0)
    {
      temp_spectrum[fft_shift(i)] = 0u;
    } else {
      const float normalised = 255.0f*(log10f(magnitude)-logmin)/(logmax-logmin);
      const float clamped = std::max(std::min(normalised, 255.0f), 0.0f);
      temp_spectrum[fft_shift(i)] = clamped;
    }
  }

  //zoom
  for(int16_t i=0; i<256; ++i)
  {
    uint16_t total = 0;
    for(int16_t j=0; j<zoom; j++)
    {
      int16_t from_idx = ((i+j-zoom/2-128)/zoom)+128;
      total += temp_spectrum[from_idx];
    }
    spectrum[i] = total/zoom;
  }

  sem_release(&spectrum_semaphore);

  //number steps representing 10dB
  dB10 = 256/(2*logf(max/min));
}

static uint16_t __time_critical_func(audio_correlate)(int16_t a[128],
                                                      int16_t b[128]) {
  int32_t s_max = INT32_MIN;
  uint16_t s_argmax = 0;

  for (uint16_t i = 0; i < 128; i++) {
    const uint16_t l = 128 - i;
    int32_t s = 0;
    for (uint16_t j = 0; j < l; j++) {
      s += (a[j] * b[i + j]) >> 15;
    }
    if (s > s_max) {
      s_max = s;
      s_argmax = i;
    }
  }
  return s_argmax;
}

void rx_dsp :: get_audio_capture(uint8_t audio[])
{
  static int16_t prev_audio[128];
  int16_t audio_tmp[128];
  int16_t audio_in[128];

  sem_acquire_blocking(&audio_semaphore);
  for (uint16_t i = 0; i < (sizeof(audio_in) / sizeof(audio_in[0])); i++) {
    audio_in[i] = audio_capture[(audio_capture_idx * 16 + i) % 128];
  }
  sem_release(&audio_semaphore);
  const uint16_t x = audio_correlate(audio_in, prev_audio);
  for (uint16_t i = 0; i < x; i++) {
    audio_tmp[i] = prev_audio[127 - x + i];
  }
  for (uint16_t i = x; i < (sizeof(audio_tmp) / sizeof(audio_tmp[0])); i++) {
    audio_tmp[i] = audio_in[i - x];
  }

  for (uint16_t i = 0; i < (sizeof(audio_tmp) / sizeof(audio_tmp[0])); i++) {
    audio[i] = 32 + 6 + (audio_tmp[i] / (32767 / 48));
    prev_audio[i] = audio_in[i];
  }
}

uint32_t rx_dsp::get_iq_buffer_level()
{
  return queue_get_level(&data_queue);
}

bool rx_dsp::get_raw_data(int16_t &i, int16_t &q)
{
  uint32_t data;
  bool success = queue_try_remove(&data_queue, &data);
  i = (data >> 16) & 0xffff;
  q = data & 0xffff;
  return success;
}

float rx_dsp::get_tuning_offset_Hz()
{

  if(frequency_count > 30000)
  {
    float average_frequency = (float)frequency_accumulator/(float)frequency_count;
    frequency_offset_Hz = (pwm_audio_sample_rate * average_frequency)/(32767.0f * decimation_rate);
    frequency_accumulator = 0;
    frequency_count = 0;
  }
  return frequency_offset_Hz;
}
