dawsonjon/PicoRX/src/memory.cpp

#include "memory.h"
#include <pico.h>
const uint32_t __in_flash() __attribute__((aligned(4096))) radio_memory[512][16] = {
{198000, 30000000, 0, 33817344, 543976513, 1684955458, 538976371, 538976288, 4294967295, 4294967295, 4294967295, 4294967295, 4294967295, 4294967295, 4294967295, 4294967295},
{1413000, 1602000, 531000, 34013952, 1109415757, 1684107122, 1953718627, 538976288, 4294967295, 4294967295, 4294967295, 4294967295, 4294967295, 4294967295, 4294967295, 4294967295},
{198000, 279000, 153000, 33817344, 1109415756, 1684107122, 1953718627, 538976288, 4294967295, 4294967295, 4294967295, 4294967295, 4294967295, 4294967295, 4294967295, 4294967295},
{2300000, 2495000, 2300000, 33817344, 824203091, 544026674, 538976288, 538976288, 4294967295, 4294967295, 4294967295, 4294967295, 4294967295, 4294967295, 4294967295, 4294967295},
{3200000, 3400000, 3200000, 33817344, 958420819, 538996016, 538976288, 538976288, 4294967295, 4294967295, 4294967295, 4294967295, 4294967295, 4294967295, 4294967295, 4294967295},
{3900000, 4000000, 3900000, 33817344, 924866387, 538996021, 538976288, 538976288, 4294967295, 4294967295, 4294967295, 4294967295, 4294967295, 4294967295, 4294967295, 4294967295},
{4750000, 4995000, 4750000, 33817344, 908089171, 538996016, 538976288, 538976288, 4294967295, 4294967295, 4294967295, 4294967295, 4294967295, 4294967295, 4294967295, 4294967295},
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
{21080000, 21149000, 21070000, 33686019, 544027953, 541807440, 538976288, 538976288, 4294967295, 4294967295, 4294967295, 4294967295, 4294967295, 4294967295, 4294967295, 4294967295},
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
};
