dawsonjon/PicoRX/src/waterfall.h

#ifndef __waterfall_h__
#define __waterfall_h__
#include <cstdint>
#include "ili934x.h"
#include "xcvr.h"
#include "settings.h"
#include "codecs/sstv_decoder_picorx.h"

enum e_aux_display_state{waterfall_active, sstv_active};

class waterfall
{

  public:
  waterfall(xcvr &_transceiver);
  ~waterfall();
  void update(s_settings& ui_settings,
                       xcvr_settings& settings, xcvr_status& status,
                       uint8_t spectrum[], uint8_t dB10, uint8_t zoom);
  void configure_display(uint8_t settings, bool invert_colours, bool invert_tft, uint8_t display_driver);
  void powerOn(bool state);

  private:
  void update_spectrum(xcvr_settings& settings, xcvr_status& status,
                       uint8_t spectrum[], uint8_t dB10, uint8_t zoom);
  e_aux_display_state m_aux_display_state = waterfall_active;
  void draw();
  uint16_t heatmap(uint8_t value, bool lighten = false, bool highlight = false);
  uint16_t dBm_to_px(float power_dBm, int16_t px);
  float S_to_dBm(int S);
  int dBm_to_S(float power_dBm);
  uint8_t waterfall_buffer[120][256];
  ILI934X *display;
  xcvr &transceiver;
  c_sstv_decoder_picorx sstv_decoder;
  bool enabled = false;
  bool power_state = true;
  bool refresh = true;
  void decode_sstv();

};

#endif
