dawsonjon/PicoRX/src/clocks_pico2.cpp

#include "clocks.h"

//A list of all the achievable frequencies in range
PLLSettings possible_frequencies[] = {
    {125000000, 1, 125, 6, 2},
    {125142857, 1, 73, 7, 1},
    {125333333, 1, 94, 3, 3},
    {126000000, 1, 126, 6, 2},
    {126666666, 1, 95, 3, 3},
    {126857142, 1, 74, 7, 1},
    {127000000, 1, 127, 6, 2},
    {127200000, 1, 106, 5, 2},
    {127500000, 1, 85, 4, 2},
    {128000000, 1, 128, 6, 2},
    {128400000, 1, 107, 5, 2},
    {128571428, 1, 75, 7, 1},
    {129000000, 1, 129, 6, 2},
    {129333333, 1, 97, 3, 3},
    {129600000, 1, 108, 5, 2},
    {130000000, 1, 130, 6, 2},
    {130285714, 1, 76, 7, 1},
    {130500000, 1, 87, 4, 2},
    {130666666, 1, 98, 3, 3},
    {130800000, 1, 109, 5, 2},
    {131000000, 1, 131, 6, 2},
    {132000000, 1, 132, 6, 2},
    {133000000, 1, 133, 6, 2},
    {133200000, 1, 111, 5, 2},
    {133333333, 1, 100, 3, 3},
    {133500000, 1, 89, 4, 2},
    {133714285, 1, 78, 7, 1},
    {134000000, 1, 67, 6, 1},
    {134400000, 1, 112, 5, 2},
    {134666666, 1, 101, 3, 3},
    {135000000, 1, 90, 4, 2},
    {135428571, 1, 79, 7, 1},
    {135600000, 1, 113, 5, 2},
    {136000000, 1, 102, 3, 3},
    {136500000, 1, 91, 4, 2},
    {136800000, 1, 114, 5, 2},
    {137142857, 1, 80, 7, 1},
    {137333333, 1, 103, 3, 3},
    {138000000, 1, 115, 5, 2},
    {138666666, 1, 104, 3, 3},
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
};

uint16_t num_possible_frequencies = sizeof(possible_frequencies)/sizeof(PLLSettings);
