dawsonjon/PicoRX/memory_loader/channel_to_words.py

#!/usr/bin/env python

#struct s_channel_settings
#{
  #uint32_t frequency;
  #uint32_t max_frequency;
  #uint32_t min_frequency;
  #uint8_t  mode;
  #uint8_t  agc_setting;
  #uint8_t  step;
  #uint8_t  bandwidth;
#};

#struct s_memory_channel
#{
  #s_channel_settings channel;
  #char label[16];
#};

modes = {
  "AM" :0,
  "AMS":1,
  "LSB":2,
  "USB":3,
  "NFM":4,
  "CW" :5
}
agc_speeds = {"FAST": 0, "NORMAL": 1, "SLOW": 2, "VERY SLOW": 3}
steps = {
    "10Hz": 0,
    "50Hz": 1,
    "100Hz": 2,
    "500Hz": 3,
    "1kHz": 4,
    "5kHz": 5,
    "6.25kHz": 6,
    "9kHz": 7,
    "10kHz": 8,
    "12.5kHz": 9,
    "25kHz": 10,
    "50kHz": 11,
    "100kHz": 12,
}
bandwidths = {
  "Very Narrow" :0,
  "Narrow":1,
  "Normal":2,
  "Wide":3,
  "Very Wide":4
}
rmodes = dict(zip(modes.values(), modes.keys()))
ragc_speeds = dict(zip(agc_speeds.values(), agc_speeds.keys()))
rsteps = dict(zip(steps.values(), steps.keys()))
rbandwidths = dict(zip(bandwidths.values(), bandwidths.keys()))

def pack(string):
    return (ord(string[0]) << 0) + (ord(string[1]) << 8) + (ord(string[2]) << 16) + (ord(string[3]) << 24)

def unpack(word):
    return chr(word >> 0 & 0xff) + chr(word >> 8 & 0xff) + chr(word >> 16 & 0xff) + chr(word >> 24 & 0xff)

def channel_to_words(name, frequency, min_frequency, max_frequency, mode, agc_speed, step, bandwidth):
    if len(name) < 16:
      name += (" "*(16-len(name)))

    #split frequency into bytes
    data = [
      int(frequency)&0xffffffff,
      int(max_frequency)&0xffffffff,
      int(min_frequency)&0xffffffff,
      (modes[mode] << 0) | (agc_speeds[agc_speed] << 8) | (steps[step] << 16) | (bandwidths[bandwidth] << 24),
      pack(name[0:4]),
      pack(name[4:8]),
      pack(name[8:12]),
      pack(name[12:16]),
      0xffffffff,
      0xffffffff,
      0xffffffff,
      0xffffffff,
      0xffffffff,
      0xffffffff,
      0xffffffff,
      0xffffffff,
    ]

    return data


def words_to_channel(words):
  name = "asdfasdfasdfsad"
  frequency = words[0]
  max_frequency = words[1]
  min_frequency = words[2]
  mode = rmodes[words[3] >> 0 & 0xff]
  agc_speed = ragc_speeds[words[3] >> 8 & 0xff]
  step = rsteps[words[3] >> 16 & 0xff]
  bandwidth = rbandwidths[words[3] >> 24 & 0xff]
  name = unpack(words[4]) + unpack(words[5]) + unpack(words[6]) + unpack(words[7])

  return name, frequency, min_frequency, max_frequency, mode, agc_speed, step, bandwidth
